electgpl/DCDCsyncBuckFSS/PCB/EMI_SS_Supply_Electgpl/EMI_SS_Supply_Electgpl2.png

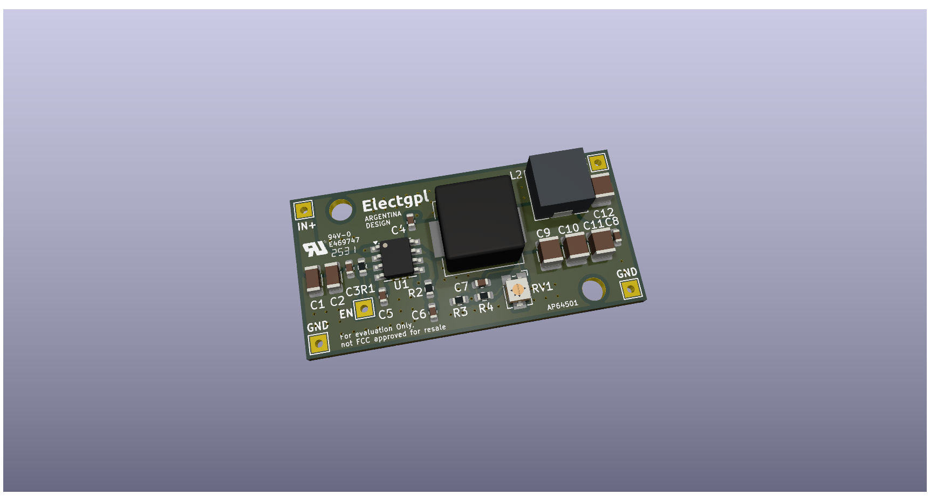
PCB/EMI_SS_Supply_Electgpl/EMI_SS_Supply_Electgpl2.png
